reynico/arduino-dds/assets/detalle_lcd.png

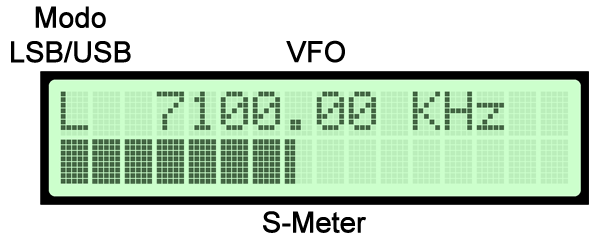
assets/detalle_lcd.png
